lab11/gap/software/nrf51822/gap.h

/* Copyright (c) 2012 Nordic Semiconductor. All Rights Reserved.
 *
 * The information contained herein is property of Nordic Semiconductor ASA.
 * Terms and conditions of usage are described in detail in NORDIC
 * SEMICONDUCTOR STANDARD SOFTWARE LICENSE AGREEMENT.
 *
 * Licensees are granted free, non-transferable use of the information. NO
 * WARRANTY of ANY KIND is provided. This heading must NOT be removed from
 * the file.
 *
 */
#ifndef PCA10001_H
#define PCA10001_H

#include "nrf_gpio.h"

#define DEVICE_NAME    "gap"


#define LED_START      13
#define LED_0          13
#define LED_1          13
#define LED_STOP       13

//#define BUTTON_START   16
//#define BUTTON_0       16
//#define BUTTON_1       17
//#define BUTTON_STOP    17
//#define BUTTON_PULL    NRF_GPIO_PIN_PULLUP

// This pin is mapped to the FTDI chip to all the device to enter the
// bootloader mode.
#define BOOTLOADER_CTRL_PIN  3
#define BOOTLOADER_CTRL_PULL NRF_GPIO_PIN_PULLUP


#define RX_PIN_NUMBER  28
#define TX_PIN_NUMBER  29
#define CTS_PIN_NUMBER 0
#define RTS_PIN_NUMBER 0
#define HWFC           false

#define SPIS_MISO_PIN  9    // SPI MISO signal.
#define SPIS_CSN_PIN   11 // 6  // SPI CSN signal.
#define SPIS_MOSI_PIN  8    // SPI MOSI signal.
#define SPIS_SCK_PIN   10   // SPI SCK signal.

#define SPIM0_SCK_PIN       9u     /**< SPI clock GPIO pin number. */
#define SPIM0_MOSI_PIN      11u     /**< SPI Master Out Slave In GPIO pin number. */
#define SPIM0_MISO_PIN      10u     /**< SPI Master In Slave Out GPIO pin number. */
#define SPIM0_SS_PIN        1u     /**< SPI Slave Select GPIO pin number. */

//#define SPIM1_SCK_PIN       16u     /**< SPI clock GPIO pin number. */
//#define SPIM1_MOSI_PIN      18u     /**< SPI Master Out Slave In GPIO pin number. */
//#define SPIM1_MISO_PIN      17u     /**< SPI Master In Slave Out GPIO pin number. */
//#define SPIM1_SS_PIN        19u     /**< SPI Slave Select GPIO pin number. */

// serialization APPLICATION board

// UART
// this configuration works with the SPI wires setup
#define SER_APP_RX_PIN              20     // UART RX pin number.
#define SER_APP_TX_PIN              22     // UART TX pin number.
#define SER_APP_CTS_PIN             23     // UART Clear To Send pin number.
#define SER_APP_RTS_PIN             21     // UART Request To Send pin number.

// SPI
#if 0
#define SER_APP_SPIM0_SCK_PIN       20     // SPI clock GPIO pin number.
#define SER_APP_SPIM0_MOSI_PIN      17     // SPI Master Out Slave In GPIO pin number
#define SER_APP_SPIM0_MISO_PIN      16     // SPI Master In Slave Out GPIO pin number
#define SER_APP_SPIM0_SS_PIN        21     // SPI Slave Select GPIO pin number
#define SER_APP_SPIM0_RDY_PIN       19     // SPI READY GPIO pin number
#define SER_APP_SPIM0_REQ_PIN       18     // SPI REQUEST GPIO pin number
#else
#define SER_APP_SPIM0_SCK_PIN       23     // SPI clock GPIO pin number.
#define SER_APP_SPIM0_MOSI_PIN      20     // SPI Master Out Slave In GPIO pin number
#define SER_APP_SPIM0_MISO_PIN      22     // SPI Master In Slave Out GPIO pin number
#define SER_APP_SPIM0_SS_PIN        21     // SPI Slave Select GPIO pin number
#define SER_APP_SPIM0_RDY_PIN       25     // SPI READY GPIO pin number
#define SER_APP_SPIM0_REQ_PIN       24     // SPI REQUEST GPIO pin number
#endif

// serialization CONNECTIVITY board

// UART
#if 0
#define SER_CON_RX_PIN              22    // UART RX pin number.
#define SER_CON_TX_PIN              20    // UART TX pin number.
#define SER_CON_CTS_PIN             21    // UART Clear To Send pin number. Not used if HWFC is set to false.
#define SER_CON_RTS_PIN             23    // UART Request To Send pin number. Not used if HWFC is set to false.
#else
// this configuration works with the SPI wires setup
#define SER_CON_RX_PIN              20    // UART RX pin number.
#define SER_CON_TX_PIN              22    // UART TX pin number.
#define SER_CON_CTS_PIN             21    // UART Clear To Send pin number. Not used if HWFC is set to false.
#define SER_CON_RTS_PIN             23    // UART Request To Send pin number. Not used if HWFC is set to false.
#endif

//SPI
#if 0
#define SER_CON_SPIS_SCK_PIN        20    // SPI SCK signal.
#define SER_CON_SPIS_MISO_PIN       16    // SPI MISO signal.
#define SER_CON_SPIS_MOSI_PIN       17    // SPI MOSI signal.
#define SER_CON_SPIS_CSN_PIN        21    // SPI CSN signal.
#define SER_CON_SPIS_RDY_PIN        19     // SPI READY GPIO pin number.
#define SER_CON_SPIS_REQ_PIN        18     // SPI REQUEST GPIO pin number.
#else
#define SER_CON_SPIS_SCK_PIN        23    // SPI SCK signal.
#define SER_CON_SPIS_MOSI_PIN       22    // SPI MOSI signal.
#define SER_CON_SPIS_MISO_PIN       20    // SPI MISO signal.
#define SER_CON_SPIS_CSN_PIN        21    // SPI CSN signal.
#define SER_CON_SPIS_RDY_PIN        25     // SPI READY GPIO pin number.
#define SER_CON_SPIS_REQ_PIN        24     // SPI REQUEST GPIO pin number.
#endif

#define SER_CONN_ASSERT_LED_PIN     LED_0

#endif
