lab11/gap/software/driver/nrf51822/debug.h

#ifndef DEBUG_H
#define DEBUG_H

// Define different levels of debug printing

// print nothing
#define DEBUG_PRINT_OFF 0
// print only when something goes wrong
#define DEBUG_PRINT_ERR 1
// print occasional messages about interesting things
#define DEBUG_PRINT_INFO 2
// print a good amount of debugging output
#define DEBUG_PRINT_DBG 3


// Define the printk macros.
#define ERR(tag, ...)  do {if (config.debug_print >= DEBUG_PRINT_ERR)  { printk(tag "[nrf51822] " __VA_ARGS__); }} while (0)
#define INFO(tag, ...) do {if (config.debug_print >= DEBUG_PRINT_INFO) { printk(tag "[nrf51822] " __VA_ARGS__); }} while (0)
#define DBG(tag, ...)  do {if (config.debug_print >= DEBUG_PRINT_DBG)  { printk(tag "[nrf51822] " __VA_ARGS__); }} while (0)

#endif
